hsynercn/DistanceSensingGlove/materials/focus/03.bmp

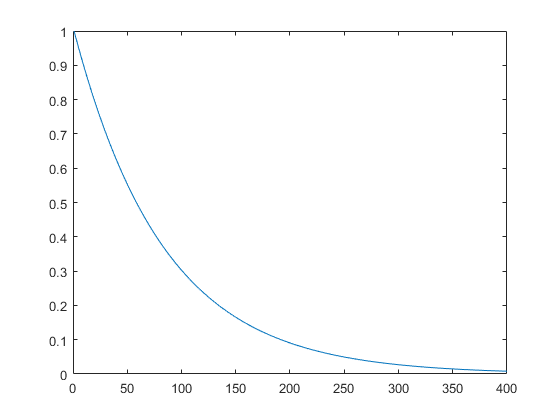
materials/focus/03.bmp
