hsynercn/DistanceSensingGlove/materials/focus/06.bmp

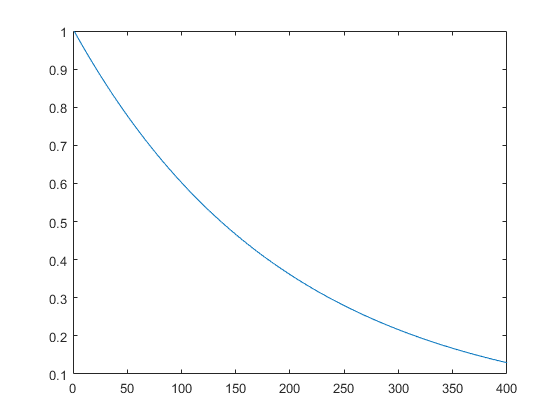
materials/focus/06.bmp
