hsynercn/DistanceSensingGlove/materials/focus/08.bmp

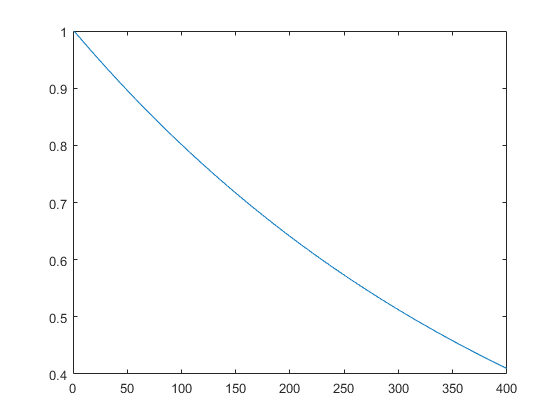
materials/focus/08.bmp
